MOSH-Insa-Toulouse/2021_2022_Grindal_Mariez/Illustrations/bode_diagram_spice.png

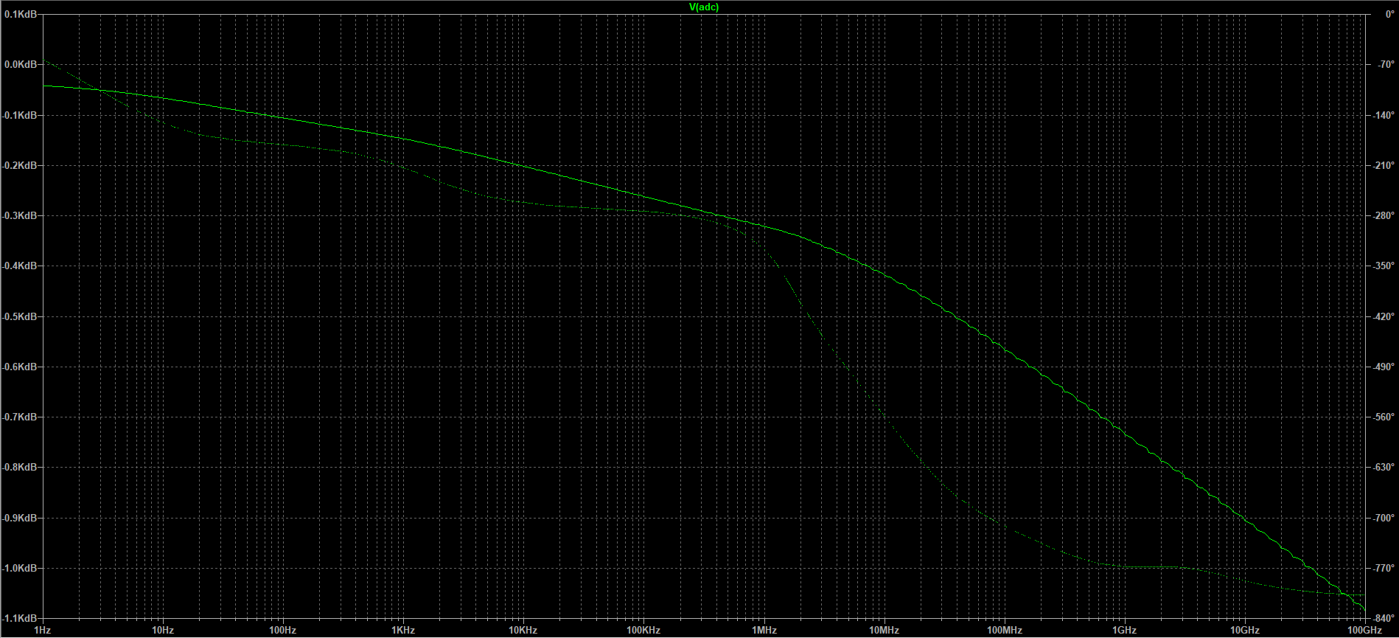
Illustrations/bode_diagram_spice.png
