MOSH-Insa-Toulouse/2021_2022_Grindal_Mariez/Electrical simulations on LT-Spice/graphite_sensor.asc

B2: bi; I=V(cp,cn)*({G0}+v(gc,gn)*{G0})
C0: cap; 200µ
R0: res; 1k
Named nets: gp, gn, cp, cn, gc
