MOSH-Insa-Toulouse/2021_2022_Grindal_Mariez/Electrical simulations on LT-Spice/Projet_grindal_mariez_elec_simulation.asc

C1: cap; 100n
C2: cap; 100n
C4: cap; 1µ
C5: cap; 100n
R1: res; 100k
R2: res; 500
R3: res; 100k
R4: res; 10k
R5: res; 1k
R6: res; {R6}
U1: LTC1050
V1: voltage; 5
V2: voltage; PULSE(0 0.01 0.2 0.1 0.1 2); AC 1 0
Named nets: 0, ADC
.tran 2
.step param R6 10k 40k 1K
