MOSH-Insa-Toulouse/2021_2022_Grindal_Mariez/Electrical simulations on LT-Spice/Projet_grindal_mariez_elec_simulation_2.asc

C1: cap; 100n
C2: cap; 100n
C3: cap; 1p
C4: cap; 1µ
R1: res; 100k
R2: res; 500
R3: res; 100k
R4: res; 10k
R5: res; 1k
R6: res; {R6}
U1: LTC1050
V1: voltage; 5
V2: voltage; SINE(0 325 50)
V3: voltage; PULSE(0 1 0.2 0.1 0.1 1); AC 1 0
X1: graphite_sensor
Named nets: 0, ADC, +5V
.param G1=10n R0=100k G0=10n
.tran 2
.step param R6 1k 15k 1k
